videojedi/esp32-s3-tally/src/certs.h

/*
    Amazon Trust Services root certificates, used to validate the S3 bucket that hosts
    firmware releases. Source: https://www.amazontrust.com/repository/
    Amazon Root CA 1-4 expire 2038-2040, Starfield Services Root G2 expires 2037.
*/
#pragma once
#include <Arduino.h>

static const char AMAZON_ROOT_CAS[] PROGMEM = R"CERTS(
-----BEGIN CERTIFICATE-----
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
rqXRfboQnoZsG4q5WTP468SQvvG5
-----END CERTIFICATE-----
-----BEGIN CERTIFICATE-----
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
4PsJYGw=
-----END CERTIFICATE-----
-----BEGIN CERTIFICATE-----
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
YyRIHN8wfdVoOw==
-----END CERTIFICATE-----
-----BEGIN CERTIFICATE-----
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
1KyLa2tJElMzrdfkviT8tQp21KW8EA==
-----END CERTIFICATE-----
-----BEGIN CERTIFICATE-----
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
sSi6
-----END CERTIFICATE-----
)CERTS";
